zakqwy/NeuroBytes/Pictures/v08_cfrp.png

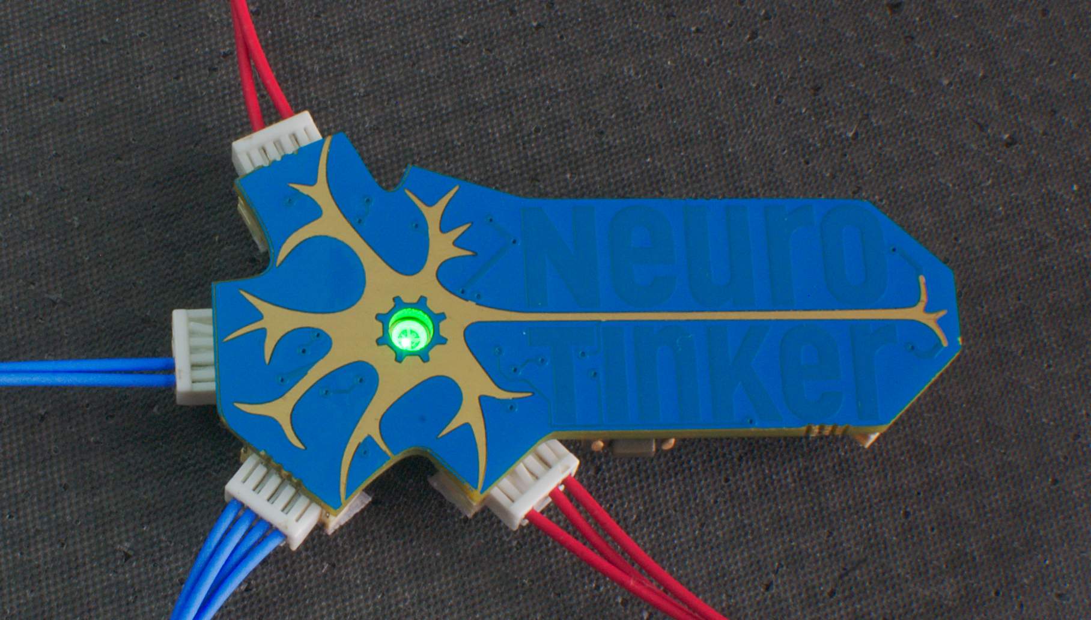
Pictures/v08_cfrp.png
